mbit237/wro-2026-galaxy-raiders-future-engineers/schemes/coind4.jpg

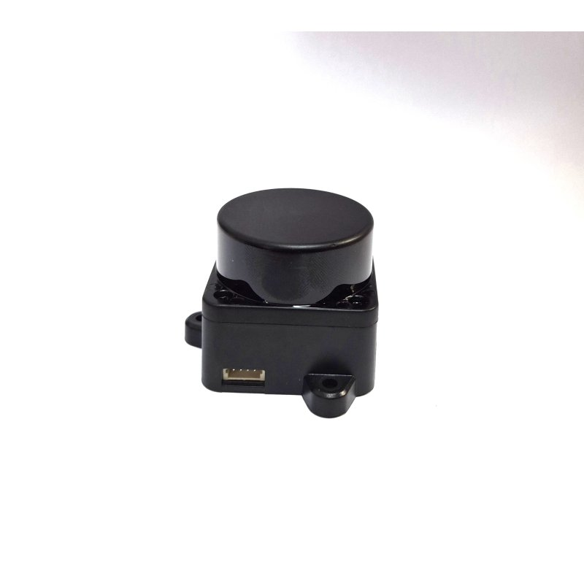
schemes/coind4.jpg
