mbit237/wro-2026-galaxy-raiders-future-engineers/schemes/Screenshot 2026-08-23 at 4.50.14 PM.png

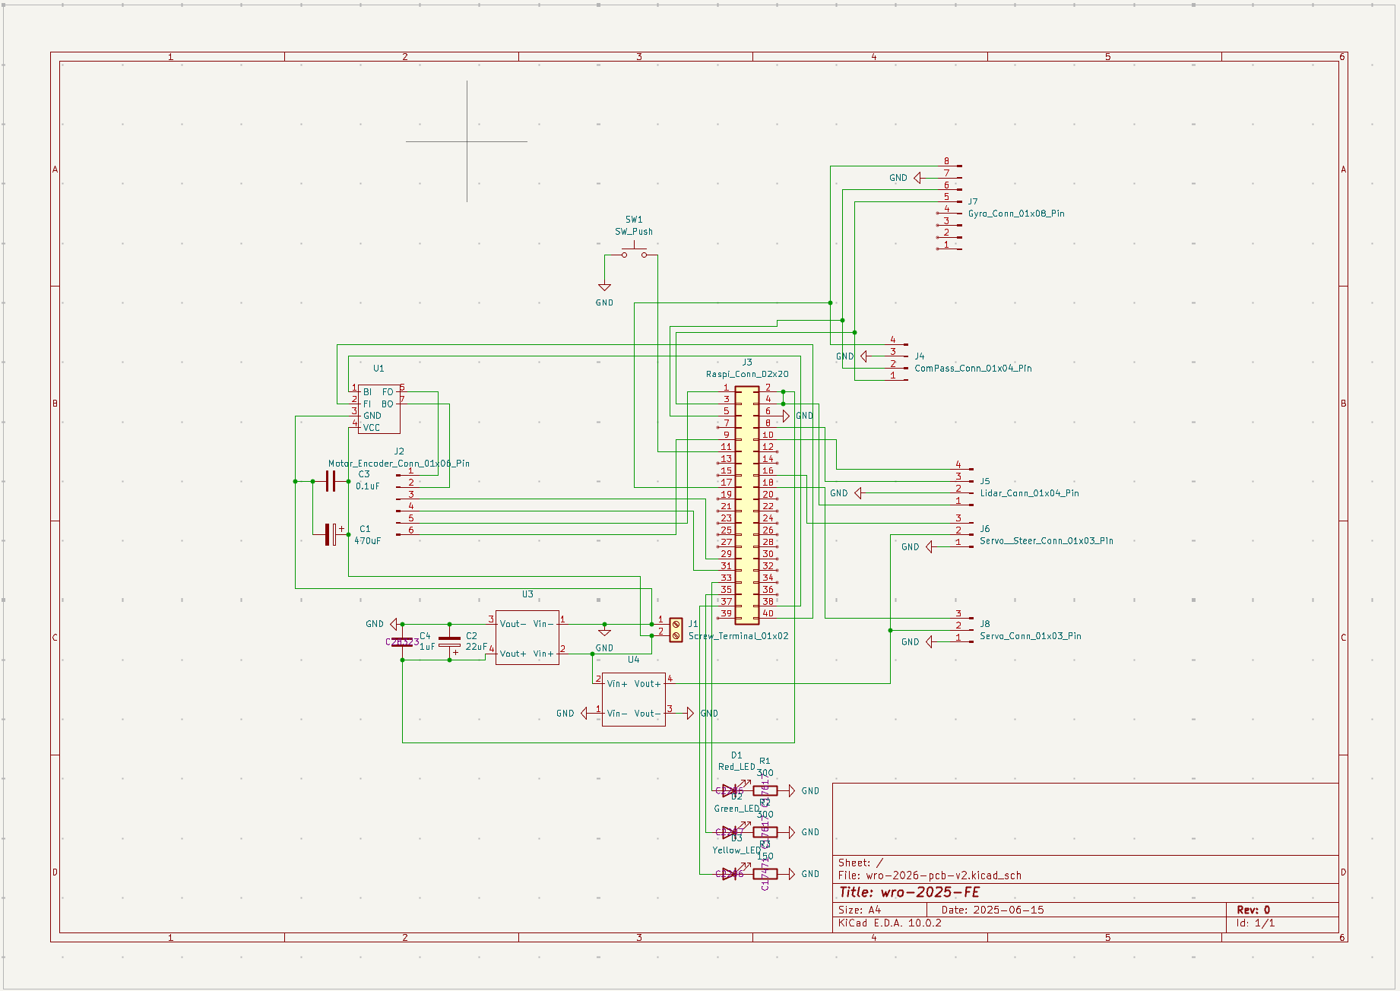
schemes/Screenshot 2026-08-23 at 4.50.14 PM.png
