mbit237/wro-2026-galaxy-raiders-future-engineers/t-photos/20250913_pic079.jpg

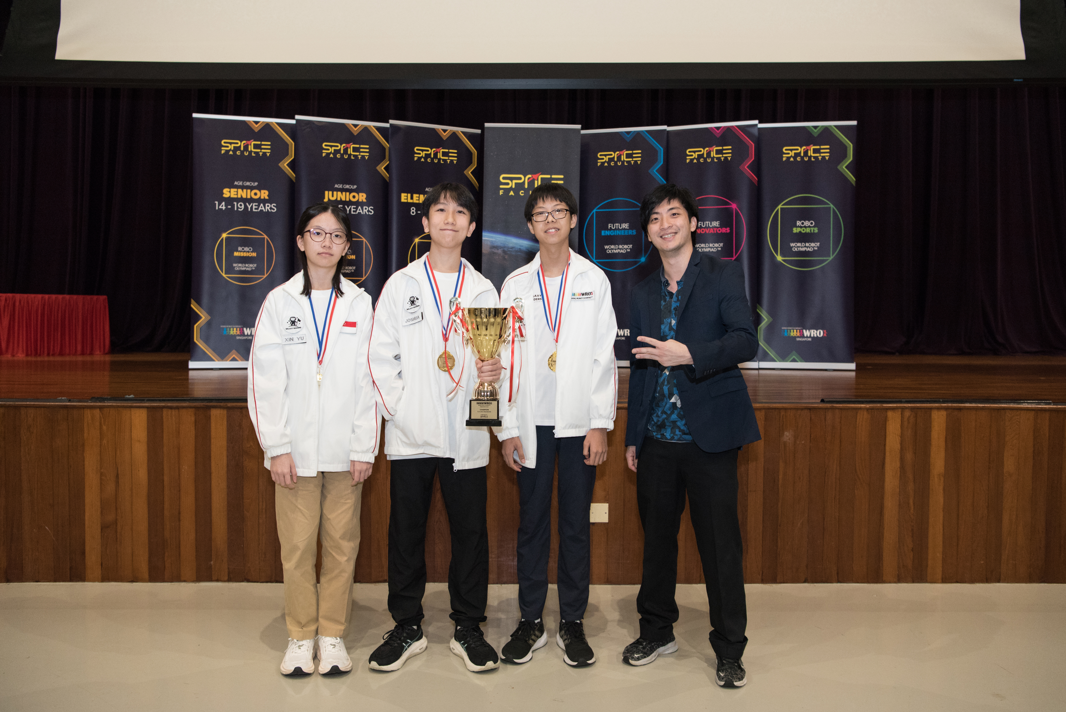
t-photos/20250913_pic079.jpg
