mbit237/wro-2026-galaxy-raiders-future-engineers/v-photos/20260816_pic011.jpg

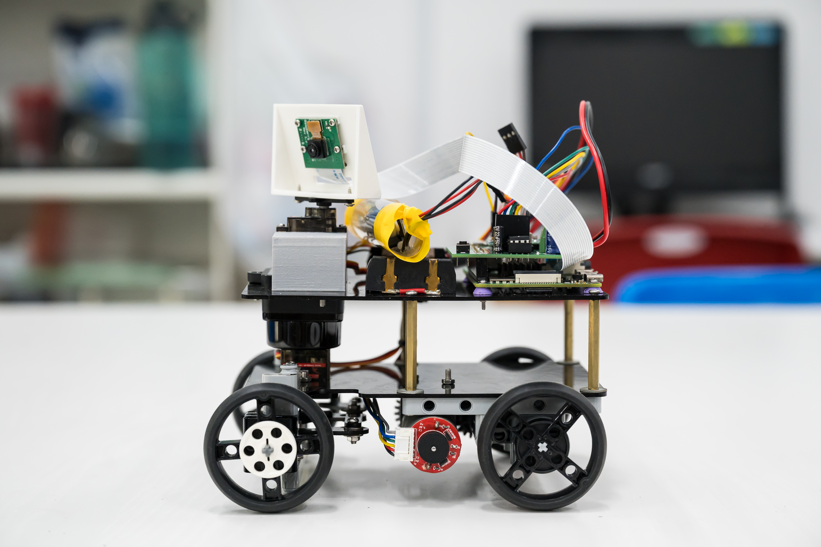
v-photos/20260816_pic011.jpg
