mbit237/wro-2026-galaxy-raiders-future-engineers/v-photos/20260816_pic016.jpg

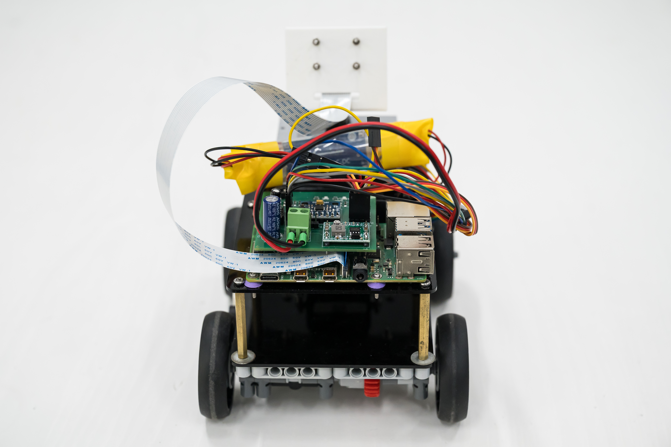
v-photos/20260816_pic016.jpg
