mbit237/wro-2026-galaxy-raiders-future-engineers/src/paths.py

import math

open_first_path = [
    [500, 300], [500, 2400]
]

cw_obstacle_first_outer_paths = [
    [[500, 1000], [500, 1210]],
    [[0, 1000], [500, 1000]],
    [[0, 1200], [300, 1200]],
]

cw_obstacle_first_inner_paths = [
    [[500, 1000], [500, 1210]],
    [[0, 1000], [500, 1000]],
    [[0, 1200], [600, 1200]],
]

ccw_obstacle_first_outer_paths = [
    # [2900, 1750], [2600, 1850]
    [[2500, 1750], [2500, 1920]],
    [[3000, 1750], [2500, 1750]],
    [[3000, 1800], [2700, 1800]],
]  
ccw_obstacle_first_inner_paths = [
    # [2900, 1750], [2400, 1850]
    [[2500, 1750], [2500, 1900]],
    [[3000, 1750], [2500, 1750]],
    [[3000, 1800], [2400, 1800]],
]

cw_parking_path = [[300, 1350], [300, 1500]]
ccw_parking_path = [[2700, 1600], [2700, 2200]]

# Open
cw_paths = [ 
    [[300, 300], [300, 2350]],
    [[300, 2700], [2350, 2700]],
    [[2700, 2700], [2700, 650]],
    [[2700, 300], [650, 300]]
]

ccw_paths = [ 
    [[2700, 300], [2700, 2350]],
    [[2700, 2700], [650, 2700]],
    [[300, 2700], [300, 650]],
    [[300, 300], [2350, 300]]
]

# Obstacle

outer_one_section = [
    # straight path #1
    [[200, 1000], [200, 1500]],

    [[200, 1500], [200, 2150]],

    [[200, 2150], [500, 2600]],

    [[800, 2700], [900, 2750]]
]

inner_one_section = [
    [[800, 1100], [800, 1500]],

    [[800, 1500], [800, 2000]], 

    [[800, 2000], [800, 2050]],

    [[950, 2200], [1100, 2200]] 
]

# Old paths

# outer_one_section = [
#     # straight path #1
#     [[200, 1000], [200, 1200]],

#     [[200, 1200], [200, 1350]],
#     # check colour
    
#     [[200, 1500], [200, 2000]], # [[200, 1500], [200, 1950]],

#     # turning point #1
#     [[200, 2000], [450, 2150.67]], # [[200, 2000], [600, 2200]],
#     # check colour
#     [[650, 2300], [650, 2346.7]], # [[700, 2400], [700, 2450]],
#     # check colour
# ]

# inner_one_section = [
#     # straight path #1
#     [[800, 1000], [800, 1200]],
#     # check colour
#     [[800, 1200], [800, 1350]], 
#     # check colour
#     #turning point #1
#     [[800, 1400], [800, 2000]],
#     [[800, 2200], [850, 2200]],
#     [[850, 2200], [1000, 2200]], # [[850, 2200], [900, 2200]],
#     # check colour
# ]

def augment_path(path):
    dx = path[1][0] - path[0][0]
    dy = path[1][1] - path[0][1]
    
    dist = math.sqrt(dx**2 + dy**2)
    path_dir = math.atan2(dy, dx) * 180 / math.pi # in degrees
    path_vec = [dx, dy]
    unit_path_vec = [path_vec[0] / dist, path_vec[1] / dist]
    p_unit_path_vec = [-1 * unit_path_vec[1], unit_path_vec[0]] 
    
    path.append(dist)
    path.append(path_dir)
    path.append(unit_path_vec)
    path.append(p_unit_path_vec)
    return path 

def augment_paths(paths):
    for p in range(len(paths)):
        paths[p] = augment_path(paths[p])
    return paths

def full_path_from_one_section(outer_one_section, inner_one_section):
    obstacle_inner_paths = inner_one_section
    obstacle_outer_paths = outer_one_section
    path_len = len(inner_one_section)
    for a in range(path_len):
        p = inner_one_section[a]
        obstacle_inner_paths.append([[p[0][1], 3000-p[0][0]], [p[1][1], 3000-p[1][0]]])
        p = outer_one_section[a]
        obstacle_outer_paths.append([[p[0][1], 3000-p[0][0]], [p[1][1], 3000-p[1][0]]])
    for a in range(path_len):
        p = inner_one_section[a]
        obstacle_inner_paths.append([[3000-p[0][0], 3000-p[0][1]], [3000-p[1][0], 3000-p[1][1]]])
        p = outer_one_section[a]
        obstacle_outer_paths.append([[3000-p[0][0], 3000-p[0][1]], [3000-p[1][0], 3000-p[1][1]]])
    for a in range(path_len):
        p = inner_one_section[a]
        obstacle_inner_paths.append([[3000-p[0][1], p[0][0]], [3000-p[1][1], p[1][0]]])
        p = outer_one_section[a]
        obstacle_outer_paths.append([[3000-p[0][1], p[0][0]], [3000-p[1][1], p[1][0]]])

    # avoid the parking wall when taking the outer paths
    # obstacle_outer_paths[0] = [[400, 1000], [400, 1200]]
    # obstacle_outer_paths[1] = [[400, 1200], [400, 1350]]
    # obstacle_outer_paths[19] = [[600, 700], [559, 700]]
    return obstacle_outer_paths, obstacle_inner_paths
    
def ccw_paths_from_cw(obstacle_outer_paths, obstacle_inner_paths):
    ccw_obstacle_inner_paths = []
    ccw_obstacle_outer_paths = []
    for a in range(len(obstacle_inner_paths)):
        p = obstacle_inner_paths[a]
        ccw_obstacle_inner_paths.append([[3000-p[0][0], p[0][1]], [3000-p[1][0], p[1][1]]])
        p = obstacle_outer_paths[a]
        ccw_obstacle_outer_paths.append([[3000-p[0][0], p[0][1]], [3000-p[1][0], p[1][1]]])

    # avoid the parking wall
    # ccw_obstacle_outer_paths[1] = [[2600, 1200], [2600, 1350]]
    # ccw_obstacle_outer_paths[2] = [[2600, 1500], [2600, 2000]]
    return ccw_obstacle_outer_paths, ccw_obstacle_inner_paths

# Open
open_first_path = augment_path(open_first_path)

cw_paths = augment_paths(cw_paths)
ccw_paths = augment_paths(ccw_paths)

# Obstacle
cw_obstacle_outer_paths, cw_obstacle_inner_paths = full_path_from_one_section(outer_one_section, inner_one_section)
cw_obstacle_outer_paths[0][0][0], cw_obstacle_outer_paths[0][1][0] = 400, 400
cw_obstacle_outer_paths[1][0][0], cw_obstacle_outer_paths[1][1][0] = 400, 400
cw_obstacle_outer_paths[-1][0][0] += 100 
cw_obstacle_outer_paths[-1][1][0] += 200
ccw_obstacle_outer_paths, ccw_obstacle_inner_paths = ccw_paths_from_cw(cw_obstacle_outer_paths, cw_obstacle_inner_paths)

ccw_obstacle_outer_paths = ccw_obstacle_outer_paths[1:] + ccw_obstacle_outer_paths[:1]
ccw_obstacle_inner_paths = ccw_obstacle_inner_paths[1:] + ccw_obstacle_inner_paths[:1]

cw_obstacle_outer_paths = augment_paths(cw_obstacle_outer_paths)
cw_obstacle_inner_paths = augment_paths(cw_obstacle_inner_paths)
cw_parking_path = augment_path(cw_parking_path)
cw_obstacle_first_inner_paths = augment_paths(cw_obstacle_first_inner_paths)
cw_obstacle_first_outer_paths = augment_paths(cw_obstacle_first_outer_paths)

ccw_obstacle_outer_paths = augment_paths(ccw_obstacle_outer_paths)
ccw_obstacle_inner_paths = augment_paths(ccw_obstacle_inner_paths)
ccw_parking_path = augment_path(ccw_parking_path)
ccw_obstacle_first_inner_paths = augment_paths(ccw_obstacle_first_inner_paths)
ccw_obstacle_first_outer_paths = augment_paths(ccw_obstacle_first_outer_paths)
