mbit237/wro-2026-galaxy-raiders-future-engineers/src/initialise_pose.py

import math

from coind4 import extract_distance_to_point

first_wall_extended = False
DIST_BUFFER = 200

def get_x(devices):
    global first_wall_extended
    while True:
        left_dist = devices["lidar"].get_distance(90)
        right_dist = devices["lidar"].get_distance(270)
        print('initial_dist (left, right): ', left_dist, right_dist)
        # Wall extended
        if 500 < left_dist + right_dist < 700: 
            first_wall_extended = True
            return ((600 - right_dist) + left_dist) / 2
        
        # Wall flushed
        elif 900 < left_dist + right_dist < 1100: 
            return ((1000 - right_dist) + left_dist) / 2

def get_y(devices):
    while True:
        fwd_dist = devices["lidar"].get_distance(0)
        rear_dist = devices["lidar"].get_distance(180)

        # both readings valid
        if 2900 < fwd_dist + rear_dist < 3100: 
            return ((3000 - fwd_dist) + rear_dist) / 2
        
        # front reading valid
        elif 1000 < fwd_dist < 2000:
            return 3000 - fwd_dist
        
        # rear reading valid
        elif 1000 < rear_dist < 2000:
            return rear_dist
        
def obstacle_on_path(devices):
    x = get_x(devices)
    y = get_y(devices)
    if y > 1500: # On the left
        x += 2000
    return [x, y, 90]

def obstacle_in_parking(devices):
    x = get_x(devices)
    if x > 500: # CCW
        x += 2000
        y = 2000 - devices["lidar"].get_distance(0)
    else: # CW
        y = 1000 + devices["lidar"].get_distance(180)
        
    return [x, y, 90]

def open(devices):
    global first_wall_extended
    x = get_x(devices)
    y = get_y(devices)
    return [x, y, 90, first_wall_extended]

def confirm_pose(pose, sensor_readings):
    global first_wall_extended

    left_dist = None
    right_dist = None

    
    left_dist = extract_distance_to_point(pose, [0, 2700], sensor_readings["lidar"])
    right_dist = extract_distance_to_point(pose, [1000, 2700], sensor_readings["lidar"])
    print("Left_dist: ", left_dist)
    print("Right dist: ", right_dist)

    if left_dist is None or right_dist is None:
        return None

    left_wall_dist = math.sqrt( (0 - pose[0]) ** 2 + (2700 - pose[1]) ** 2)
    right_wall_dist = math.sqrt( (1000 - pose[0]) ** 2 + (2700 - pose[1]) ** 2)

    print("Supposed left dist wall: ", left_wall_dist)
    print("Supposed right dist wall: ", right_wall_dist)

    # Left side is empty space -- CCW
    if left_dist > left_wall_dist + DIST_BUFFER and right_dist <= right_wall_dist + DIST_BUFFER: 
        if first_wall_extended:
            pose[0] += 2400
        else:
            pose[0] += 2000
    # Invalid values
    elif (left_dist > left_wall_dist + DIST_BUFFER and right_dist > right_wall_dist + DIST_BUFFER) \
        or (left_dist <= left_wall_dist + DIST_BUFFER and right_dist <= right_wall_dist + DIST_BUFFER):
        return None
    
    return pose

    # If none of the conditions are satisfied, rerun the extract distances

# Challenges
# - Fwd and back dist were invalid because they were too far away 
#   - only look at one of the readings, discard the invalid 
#   - if both are invalid, keep reading it until it returns at least one valid reading
# - Hard to determine left or right, especially when it is close to the inner wall
#   so it is unable to detect spikes on inner corners 
#   - Defer decision: Assume it is on the left or right 
#   - Move forward to determine if it is on the left or right
