mbit237/wro-2026-galaxy-raiders-future-engineers/src/odometry.py

import time
import math

MM_PER_STEPS = 0.475 
LIDAR_WHEEL_DIST = 109

prev_steps_count = 0 
prev_z = 0 
prev_time = 0

def reset_pose():
    global prev_steps_count, prev_z, prev_time
    prev_steps_count = 0
    prev_z = 0
    prev_time = time.time()

def estimate_pose(pose, sensor_readings):
    global prev_steps_count, prev_z, prev_time

    delta_z = sensor_readings["gyro"]
    curr_steps_count = sensor_readings["encoder"]
    dist_travelled = (curr_steps_count - prev_steps_count) * MM_PER_STEPS # distance travelled since last estimate (in mm)
    prev_steps_count = curr_steps_count

    now = time.time()
    delta = now - prev_time
    prev_time = now
    
    #adding the change in gyro heading to previous pose heading
    theta = (delta_z + prev_z) / 2 / 131 * delta # tune rate of rotation (131)
    curr_heading = theta + pose[2]  # current heading in degrees
    prev_z = delta_z  # update previous z for next iteration

    # calculate heading and perpendicular vectors for initial position
    v1 = [math.cos(math.radians(pose[2])), math.sin(math.radians(pose[2]))]
    v2 = [v1[1], -v1[0]]  # rotate 90 degrees for dx

    # calculate initial pose of rear wheels
    wheel_pose = [pose[0] - LIDAR_WHEEL_DIST * v1[0], pose[1] - LIDAR_WHEEL_DIST * v1[1], pose[2]]
    # print("Wheel pose:", wheel_pose)

    if theta < 0.001 and theta > -0.001:  # if theta is too small, don't change pose
        dx = 0
        dy = dist_travelled
    else:
        theta = math.radians(theta)  # convert to radians
        r = dist_travelled / theta
        dy = r * math.sin(theta)  # change in y
        dx = r * math.cos(theta) - r # change in x, final - initial 

    x = wheel_pose[0] + v1[0] * dy + v2[0] * dx 
    y = wheel_pose[1] + v1[1] * dy + v2[1] * dx

    # print("X:", x, "Y:", y)

    # calculate final heading vector
    curr_heading_rad = math.radians(curr_heading)
    v3 = [math.cos(curr_heading_rad), math.sin(curr_heading_rad)]

    # shifted pose back to lidar pose 
    x_final = x + LIDAR_WHEEL_DIST * v3[0] 
    y_final = y + LIDAR_WHEEL_DIST * v3[1]
    # print("Final pose:", [x_final, y_final, curr_heading])

    return [x_final, y_final, curr_heading]
