mbit237/wro-2026-galaxy-raiders-future-engineers/src/point_cloud_test.py

import time
from point_cloud_localisation import *
                # x, y, heading
actual_pose = [2557.221145629883, 2535.240325927734, 10.297032712854872]

lidar_readings = [[360, 450.03142218069206], [359, 448.67661554748315], [358, 447.4658349372825], [357, 446.39718226026014], [356, 445.46899305534555], [355, 444.67982801499556], [354, 444.02847054519816], [353, 443.51391948853717], [352, 443.13538652379077], [351, 442.8922937389767], [350, 442.78426967260975], [349, 442.81115007861047], [348, 442.97297559649576], [347, 443.2699935381952], [346, 443.702656687051], [345, 444.27162678956427], [344, 444.9777767456795], [343, 445.8221924031889], [342, 446.8061800742803], [341, 447.93126804149153], [340, 449.1992102226284], [339, 450.6120020039176], [338, 452.171876687903], [337, 453.8813287099306], [336, 455.7431068049343], [335, 457.7602302199184], [334, 459.93601492487124], [333, 462.2740651594663], [332, 464.7783135960983], [331, 467.45299671725854], [330, 470.3027410804637], [329, 473.3325042878536], [328, 476.5476626320658], [327, 479.95399878264595], [326, 483.5577325350897], [325, 487.36557442857213], [324, 491.3847288054277], [323, 495.6229656955688], [322, 500.08858804284154], [321, 504.7905754276689], [320, 509.738585526211], [319, 514.9429431614685], [318, 520.4148511458673], [317, 526.1662798562882], [316, 532.2101936608025], [315, 538.5605096956748], [314, 545.2322874497264], [313, 552.2417882993325], [312, 559.6065325263718], [311, 567.3455435236733], [310, 575.4793264601811], [309, 584.0302510824379], [308, 593.022451066211], [307, 602.482274355885], [306, 612.4384142968485], [305, 622.9220375618818], [304, 633.967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
13, 482.09735344585283], [12, 478.57306697401043], [11, 475.24365307764424], [10, 472.103055115802], [9, 469.1456593594402], [8, 466.36626443629785], [7, 463.7600383336565], [6, 461.3225231503713], [5, 459.04959694868796], [4, 456.9374627607109], [3, 454.9826343560357], [2, 453.18191540527437], [1, 451.5323931347513]]


sensor_readings = {"lidar": lidar_readings}
curr_pose = [2500, 2500, 12]

# point_cloud_pose = localise(fake_pose, sensor_readings)
# print(f"actual pose: {actual_pose}, point_cloud_pose: {point_cloud_pose}")
# point_cloud_pose = localise(point_cloud_pose, sensor_readings)
# print(f"actual pose: {actual_pose}, point_cloud_pose: {point_cloud_pose}")

start_time = time.perf_counter()
for x in range(1): 
    point_cloud_pose_iter = localise(curr_pose, sensor_readings, "open")

print(f"actual pose: {actual_pose}, point_cloud_pose: {point_cloud_pose_iter}")
end_time = time.perf_counter()
time_taken = end_time - start_time
print(start_time, end_time, time_taken)
